giuliobosco/domotics/diari/modello.md

# Domotics | Diario di lavoro - 13.02.2019

##### Ruberto Mattia, Paolo Guebeli, Bosco Giulio

### Canobbio, 13.02.2019

## Lavori svolti
Oggi ho fatto il Gantt

|Orario |Lavoro svolto |
|---|---|
|8:15 - 9:50 |Installato blablabla |
|10:05 - 11:00 |Migliorato documentazione |
|... |ciao |

##  Problemi riscontrati e soluzioni adottate

##  Punto della situazione rispetto alla pianificazione

## Programma di massima per la prossima giornata di lavoro
