giuliobosco/domotics/doc/img/jdbc/jdbc_uml.jpg

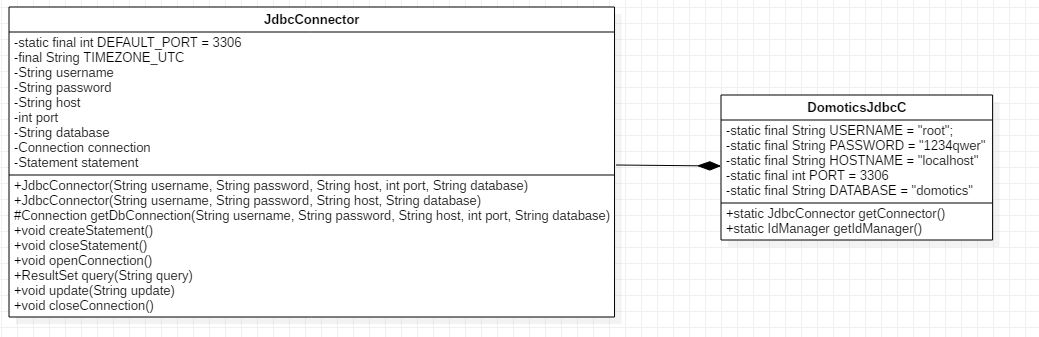
doc/img/jdbc/jdbc_uml.jpg
