giuliobosco/domotics/web/assets/img/2.jpg

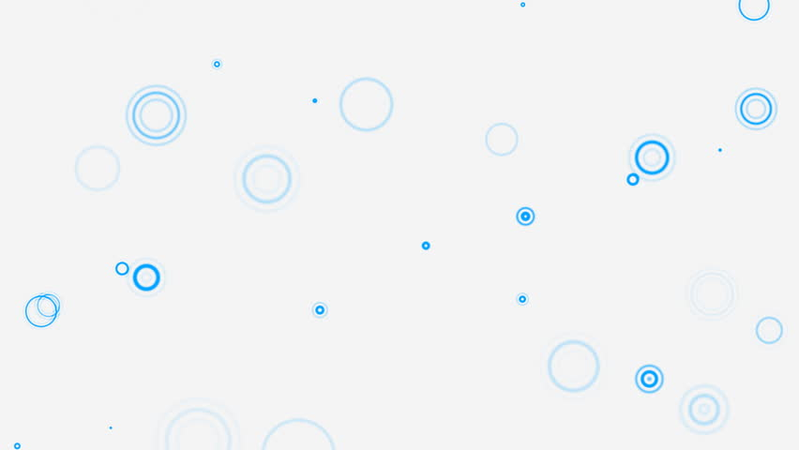
web/assets/img/2.jpg
