giuliobosco/domotics/web/assets/img/3.png

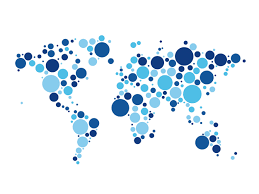
web/assets/img/3.png
