giuliobosco/domotics/web/assets/img/bg1.png

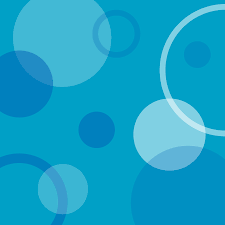
web/assets/img/bg1.png
