giuliobosco/domotics/web/assets/img/settings.png

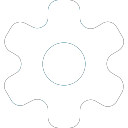
web/assets/img/settings.png
